Synthron/S65/Hardware/modules/Bus_Card/modules_3d/LPT.step

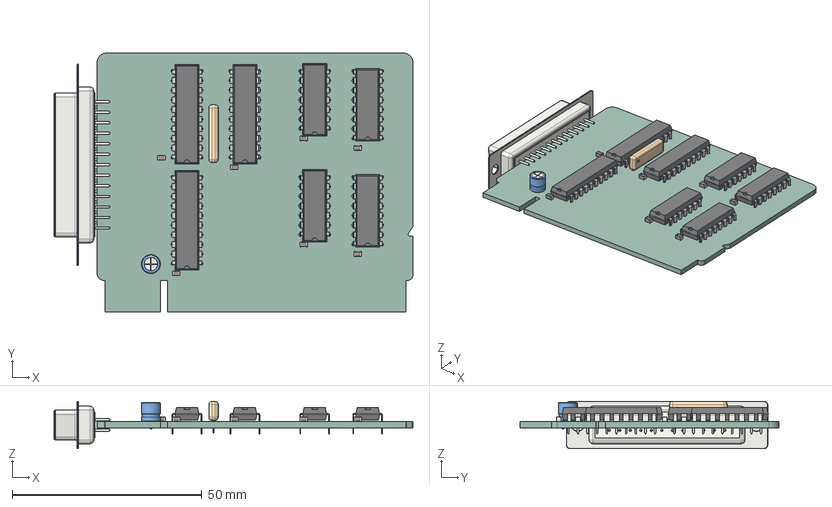
[picture p15: CAD file, 2024-07-26]
Hardware/modules/Bus_Card/modules_3d/LPT.step
94.6 x 68.2 x 12.5 mm
C_0805_2012Metric x 7
DIP-20_W7.62mm x 3
DIP-16_W7.62mm x 2
DIP-14_W7.62mm x 2
R_Array_SIP6
CP_Radial_D50mm_P250mm
DSUB-25_Female_Vertical_P2.77x2.84mm
LPT_PCB
