Synthron/S65/Hardware/modules/Bus_Card/modules_3d/CPU.step

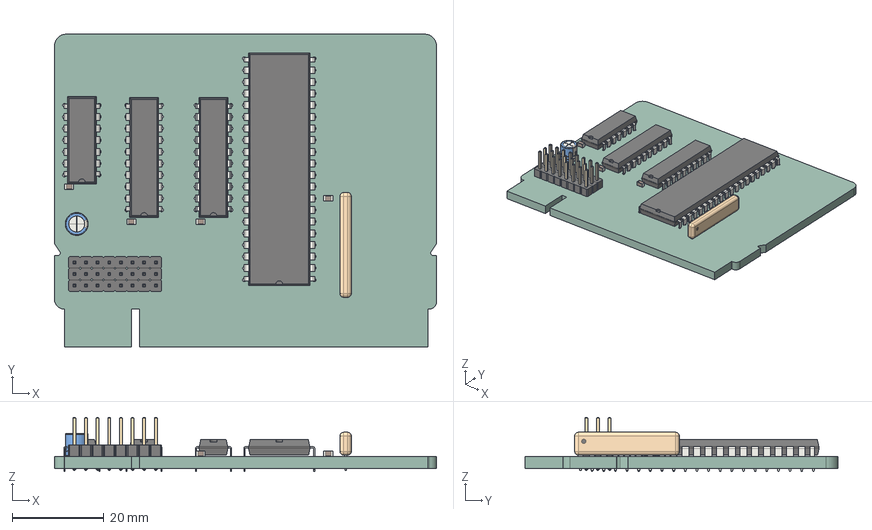
[picture p16: CAD file, 2024-07-26]
Hardware/modules/Bus_Card/modules_3d/CPU.step
83.3 x 68.2 x 11.8 mm
PinHeader_1x08_P254mm_Vertical x 3
DIP-40_W15.24mm
C_0805_2012Metric x 4
CP_Radial_D50mm_P250mm
DIP-20_W7.62mm x 2
DIP-14_W7.62mm
R_Array_SIP9
CPU_PCB
