Synthron/S65/Hardware/modules/IDE-Simple/IDE-Simple.kicad_pcb

## KiCad design Hardware/modules/IDE-Simple/IDE-Simple.kicad_pcb (2024-07-26)

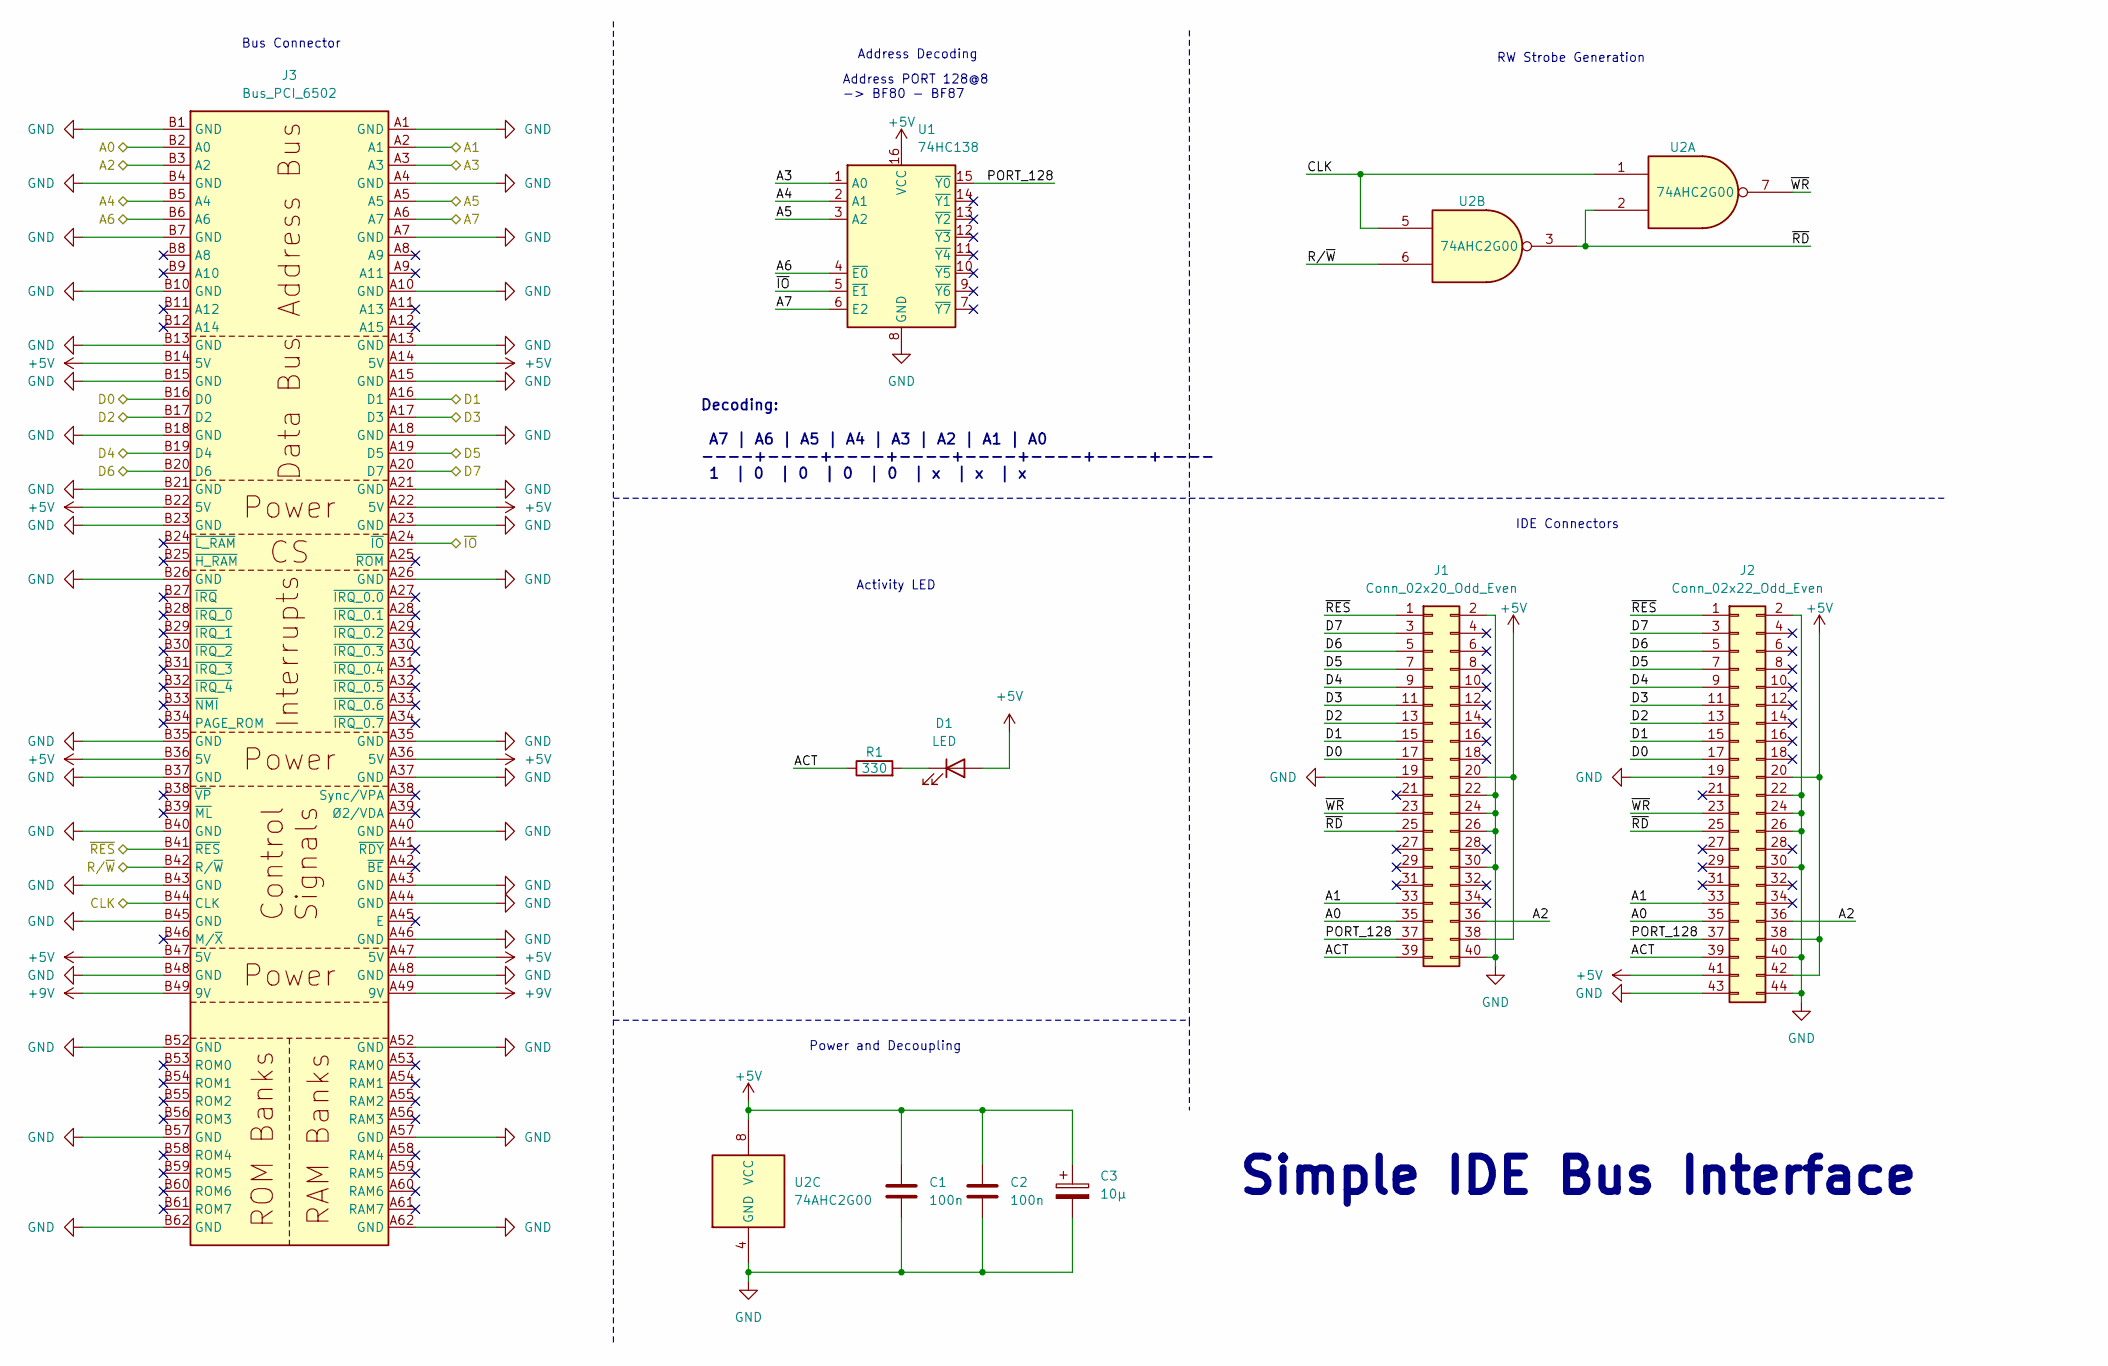
[picture p40: schematic IDE-Simple.kicad_sch, S65xx Computer System]

Parts:
C1, C2: 100n; C_0805_2012Metric
C3: 10µ; CP_Radial_D5.0mm_P2.50mm
D1: LED; LED_0805_2012Metric
J1: Conn_02x20_Odd_Even; IDC-Header_2x20_P2.54mm_Vertical
J2: Conn_02x22_Odd_Even; PinHeader_2x22_P2.00mm_Vertical
J3: Bus_PCI_6502; BUS_PCI
R1: 330; R_0805_2012Metric
U1: 74HC138; DIP-16_W7.62mm
U2: 74AHC2G00; TSSOP-8_3x3mm_P0.65mm

Connections:
+5V: C1.1, C2.1, C3.1, D1.2 (A), J1.20, J1.38, J2.20, J2.38, J2.41, J2.42, J3.A14 (5V), J3.A22 (5V), J3.A36 (5V), J3.A47 (5V), J3.B14 (5V), J3.B22 (5V), J3.B36 (5V), J3.B47 (5V), U1.16 (VCC), U2.8 (VCC)
+9V: J3.A49 (9V), J3.B49 (9V)
/A0: J1.35, J2.35, J3.B2 (A0)
/A1: J1.33, J2.33, J3.A2 (A1)
/A2: J1.36, J2.36, J3.B3 (A2)
/A3: J3.A3, U1.1 (A0)
/A4: J3.B5 (A4), U1.2 (A1)
/A5: J3.A5, U1.3 (A2)
/A6: J3.B6 (A6), U1.4 (~E0)
/A7: J3.A6 (A7), U1.6 (E2)
/ACT: J1.39, J2.39, R1.1
/CLK: J3.B44 (CLK), U2.1, U2.5
/D0: J1.17, J2.17, J3.B16 (D0)
/D1: J1.15, J2.15, J3.A16 (D1)
/D2: J1.13, J2.13, J3.B17 (D2)
/D3: J1.11, J2.11, J3.A17 (D3)
/D4: J1.9, J2.9, J3.B19 (D4)
/D5: J1.7, J2.7, J3.A19 (D5)
/D6: J1.5, J2.5, J3.B20 (D6)
/D7: J1.3, J2.3, J3.A20 (D7)
/PORT_128: J1.37, J2.37, U1.15 (~Y0)
/R/~W: J3.B42 (R/~W), U2.6
/~IO: J3.A24 (~IO), U1.5 (~E1)
/~RD: J1.25, J2.25, U2.2, U2.3
/~RES: J1.1, J2.1, J3.B41 (~RES)
/~WR: J1.23, J2.23, U2.7
GND: C1.2, C2.2, C3.2, J1.2, J1.19, J1.22, J1.24, J1.26, J1.30, J1.40, J2.2, J2.19, J2.22, J2.24, J2.26, J2.30, J2.40, J2.43, J2.44, J3.A1 (GND), J3.A4 (GND), J3.A7 (GND), J3.A10 (GND), J3.A13 (GND), J3.A15 (GND), J3.A18 (GND), J3.A21 (GND), J3.A23 (GND), J3.A26 (GND), J3.A35 (GND), J3.A37 (GND), J3.A40 (GND), J3.A43 (GND), J3.A44 (GND), J3.A46 (GND), J3.A48 (GND), J3.A52 (GND), J3.A57 (GND), J3.A62 (GND), J3.B1 (GND), J3.B4 (GND), J3.B7 (GND), J3.B10 (GND), J3.B13 (GND), J3.B15 (GND), J3.B18 (GND), J3.B21 (GND), J3.B23 (GND), J3.B26 (GND), J3.B35 (GND), J3.B37 (GND), J3.B40 (GND), J3.B43 (GND), J3.B45 (GND), J3.B48 (GND), J3.B52 (GND), J3.B57 (GND), J3.B62 (GND), U1.8 (GND), U2.4 (GND)

Notes on the sheet:
Address Decoding
Activity LED
Bus Connector
Address PORT 128@8 -> BF80 - BF87
Power and Decoupling
Decoding: A7 | A6 | A5 | A4 | A3 | A2 | A1 | A0 ----+----+----+----+----+----+----+---- 1 | 0 | 0 | 0 | 0 | x | x | x
IDE Connectors
RW Strobe Generation
Simple IDE Bus Interface

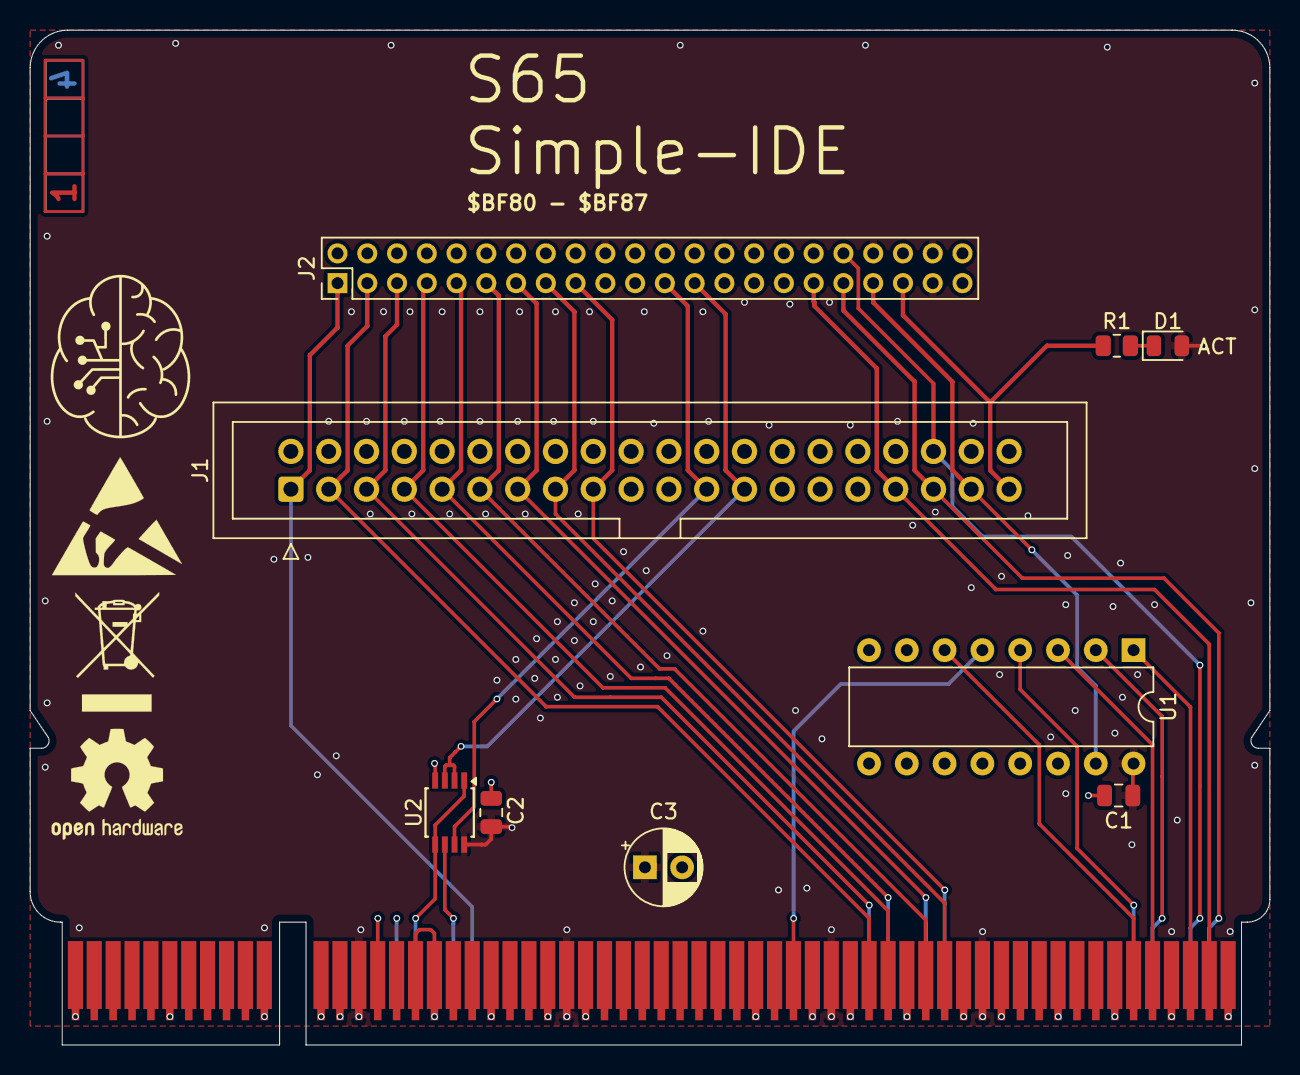
[picture p41: board IDE-Simple.kicad_pcb from above]

Board: 4 copper layers, 83.3 x 68.2 mm, 11 parts (1 on the bottom side), 27 nets.

Other parts of the board:
Ref**: Val**; ladder_4
