Synthron/S65/Hardware/modules/CF/CF.kicad_pcb

## KiCad design Hardware/modules/CF/CF.kicad_pcb (2024-07-26)

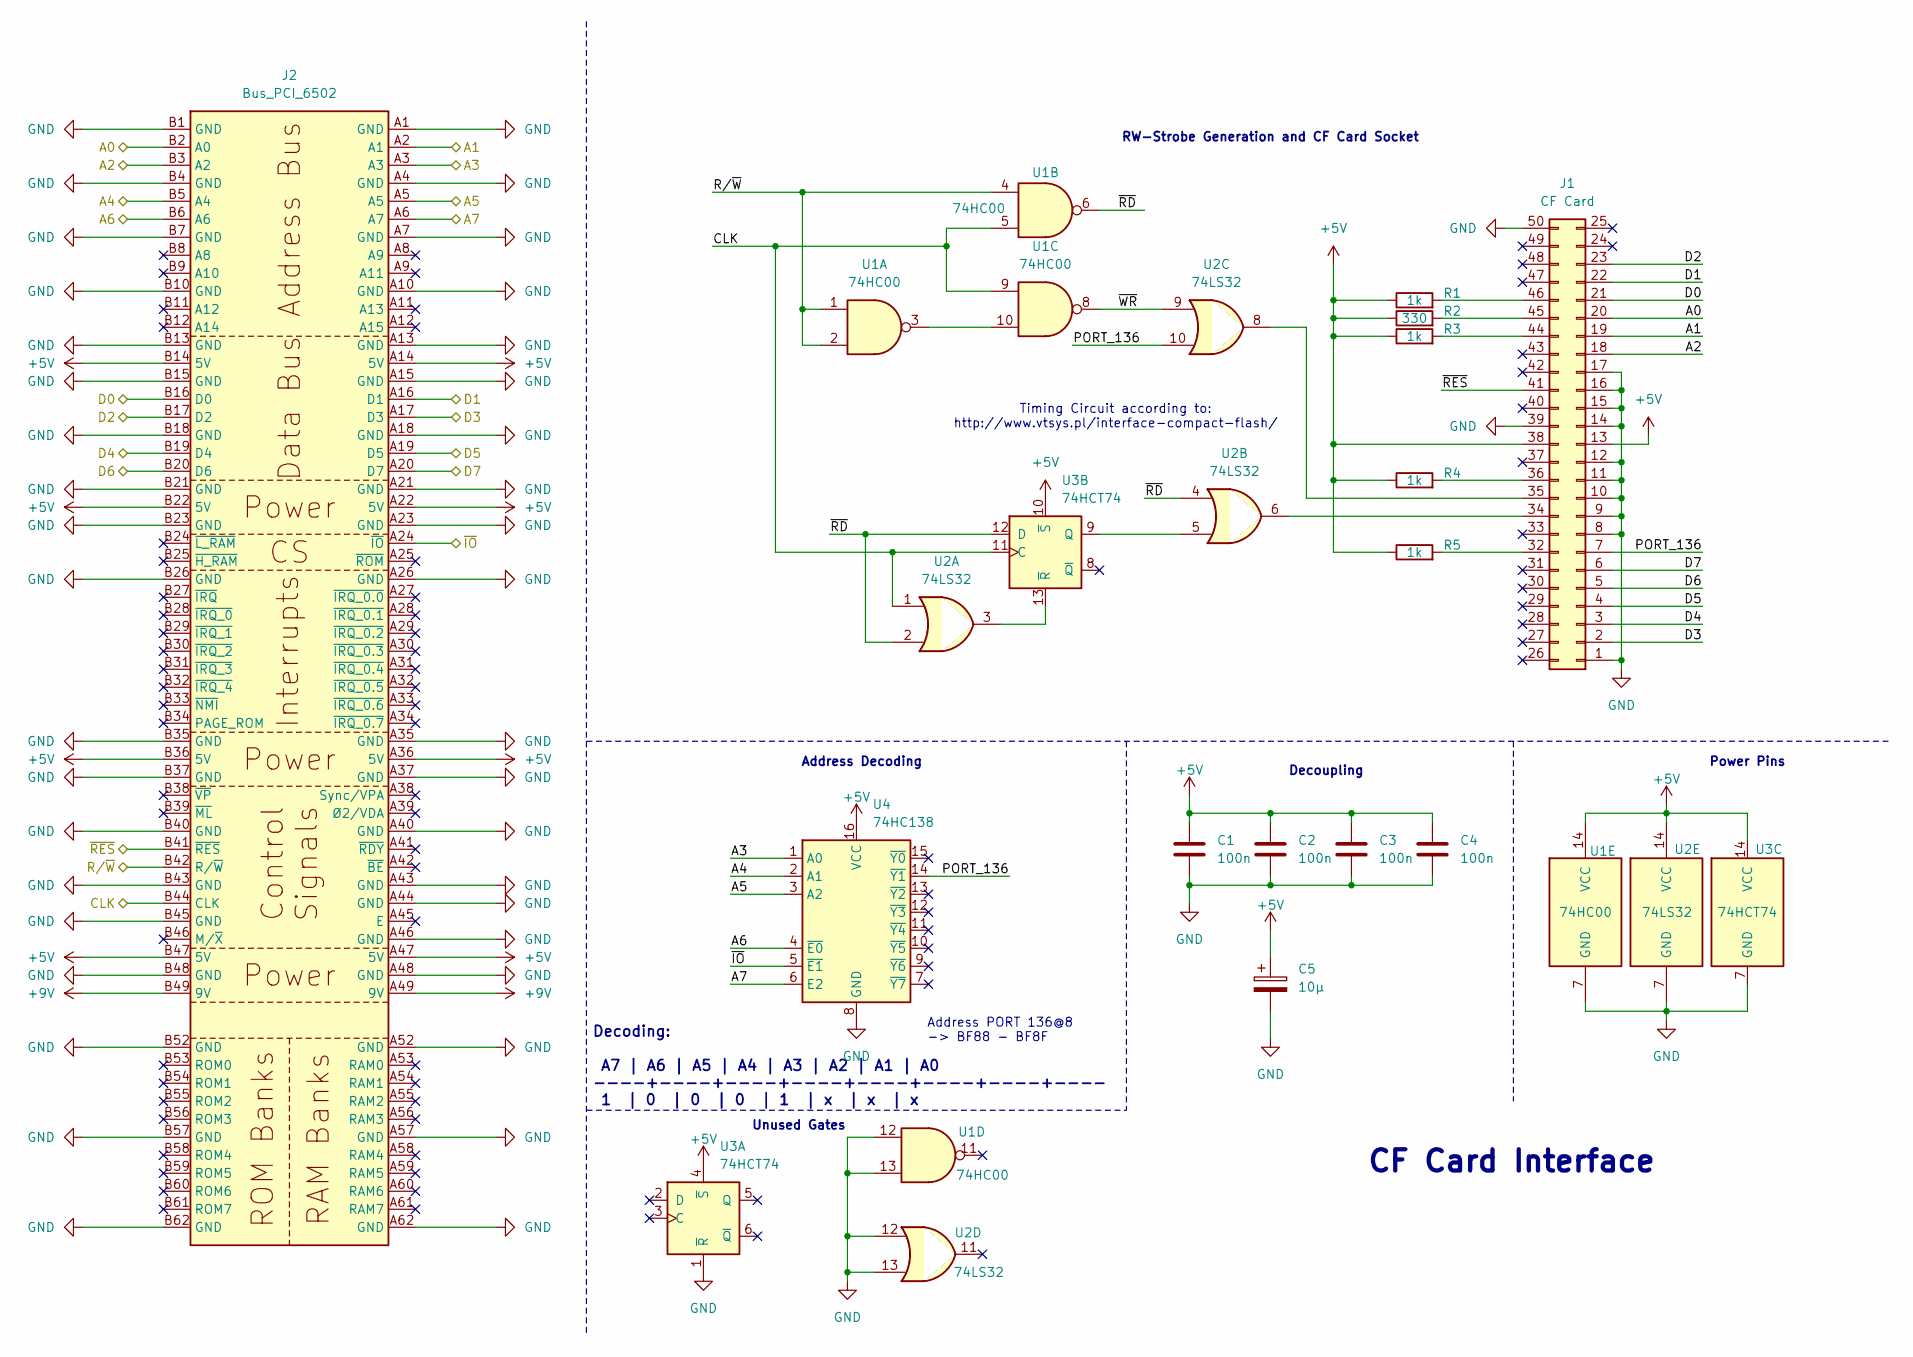
[picture p42: schematic CF.kicad_sch, S65xx Computer System]

Parts:
C1, C2, C3, C4: 100n; C_0805_2012Metric
C5: 10µ; CP_Radial_D5.0mm_P2.50mm
J1: CF Card; CF-Card_3M_N7E50-A516xx-30
J2: Bus_PCI_6502; BUS_PCI
R1, R3, R4, R5: 1k; R_0805_2012Metric
R2: 330; R_0805_2012Metric
U1: 74HC00; DIP-14_W7.62mm
U2: 74LS32; DIP-14_W7.62mm
U3: 74HCT74; DIP-14_W7.62mm
U4: 74HC138; DIP-16_W7.62mm

Connections:
+5V: C1.1, C2.1, C3.1, C4.1, C5.1, J1.13, J1.38, J2.A14 (5V), J2.A22 (5V), J2.A36 (5V), J2.A47 (5V), J2.B14 (5V), J2.B22 (5V), J2.B36 (5V), J2.B47 (5V), R1.1, R2.1, R3.1, R4.1, R5.1, U1.14 (VCC), U2.14 (VCC), U3.4 (~S), U3.10 (~S), U3.14 (VCC), U4.16 (VCC)
+9V: J2.A49 (9V), J2.B49 (9V)
/A0: J1.20, J2.B2 (A0)
/A1: J1.19, J2.A2 (A1)
/A2: J1.18, J2.B3 (A2)
/A3: J2.A3, U4.1 (A0)
/A4: J2.B5 (A4), U4.2 (A1)
/A5: J2.A5, U4.3 (A2)
/A6: J2.B6 (A6), U4.4 (~E0)
/A7: J2.A6 (A7), U4.6 (E2)
/CLK: J2.B44 (CLK), U1.5, U1.9, U2.1, U3.11 (C)
/D0: J1.21, J2.B16 (D0)
/D1: J1.22, J2.A16 (D1)
/D2: J1.23, J2.B17 (D2)
/D3: J1.2, J2.A17 (D3)
/D4: J1.3, J2.B19 (D4)
/D5: J1.4, J2.A19 (D5)
/D6: J1.5, J2.B20 (D6)
/D7: J1.6, J2.A20 (D7)
/PORT_136: J1.7, U2.10, U4.14 (~Y1)
/R/~W: J2.B42 (R/~W), U1.1, U1.2, U1.4
/~IO: J2.A24 (~IO), U4.5 (~E1)
/~RD: U1.6, U2.2, U2.4, U3.12 (D)
/~RES: J1.41, J2.B41 (~RES)
/~WR: U1.8, U2.9
GND: C1.2, C2.2, C3.2, C4.2, C5.2, J1.1, J1.8, J1.9, J1.10, J1.11, J1.12, J1.14, J1.15, J1.16, J1.17, J1.39, J1.50, J2.A1 (GND), J2.A4 (GND), J2.A7 (GND), J2.A10 (GND), J2.A13 (GND), J2.A15 (GND), J2.A18 (GND), J2.A21 (GND), J2.A23 (GND), J2.A26 (GND), J2.A35 (GND), J2.A37 (GND), J2.A40 (GND), J2.A43 (GND), J2.A44 (GND), J2.A46 (GND), J2.A48 (GND), J2.A52 (GND), J2.A57 (GND), J2.A62 (GND), J2.B1 (GND), J2.B4 (GND), J2.B7 (GND), J2.B10 (GND), J2.B13 (GND), J2.B15 (GND), J2.B18 (GND), J2.B21 (GND), J2.B23 (GND), J2.B26 (GND), J2.B35 (GND), J2.B37 (GND), J2.B40 (GND), J2.B43 (GND), J2.B45 (GND), J2.B48 (GND), J2.B52 (GND), J2.B57 (GND), J2.B62 (GND), U1.7 (GND), U1.12, U1.13, U2.7 (GND), U2.12, U2.13, U3.1 (~R), U3.7 (GND), U4.8 (GND)
unnamed: J1.32, R5.2
unnamed: J1.34, U2.6
unnamed: J1.35, U2.8
unnamed: J1.36, R4.2
unnamed: J1.44, R3.2
unnamed: J1.45, R2.2
unnamed: J1.46, R1.2
unnamed: U1.3, U1.10
unnamed: U2.5, U3.9 (Q)
unnamed: U2.3, U3.13 (~R)

Notes on the sheet:
Decoding: A7 | A6 | A5 | A4 | A3 | A2 | A1 | A0 ----+----+----+----+----+----+----+---- 1 | 0 | 0 | 0 | 1 | x | x | x
Power Pins
Address Decoding
Decoupling
CF Card Interface
Address PORT 136@8 -> BF88 - BF8F
Timing Circuit according to: http://www.vtsys.pl/interface-compact-flash/
RW-Strobe Generation and CF Card Socket
Unused Gates
