Synthron/S65/Hardware/modules/CF/CF.kicad_pcb

## KiCad design Hardware/modules/CF/CF.kicad_pcb (continued)

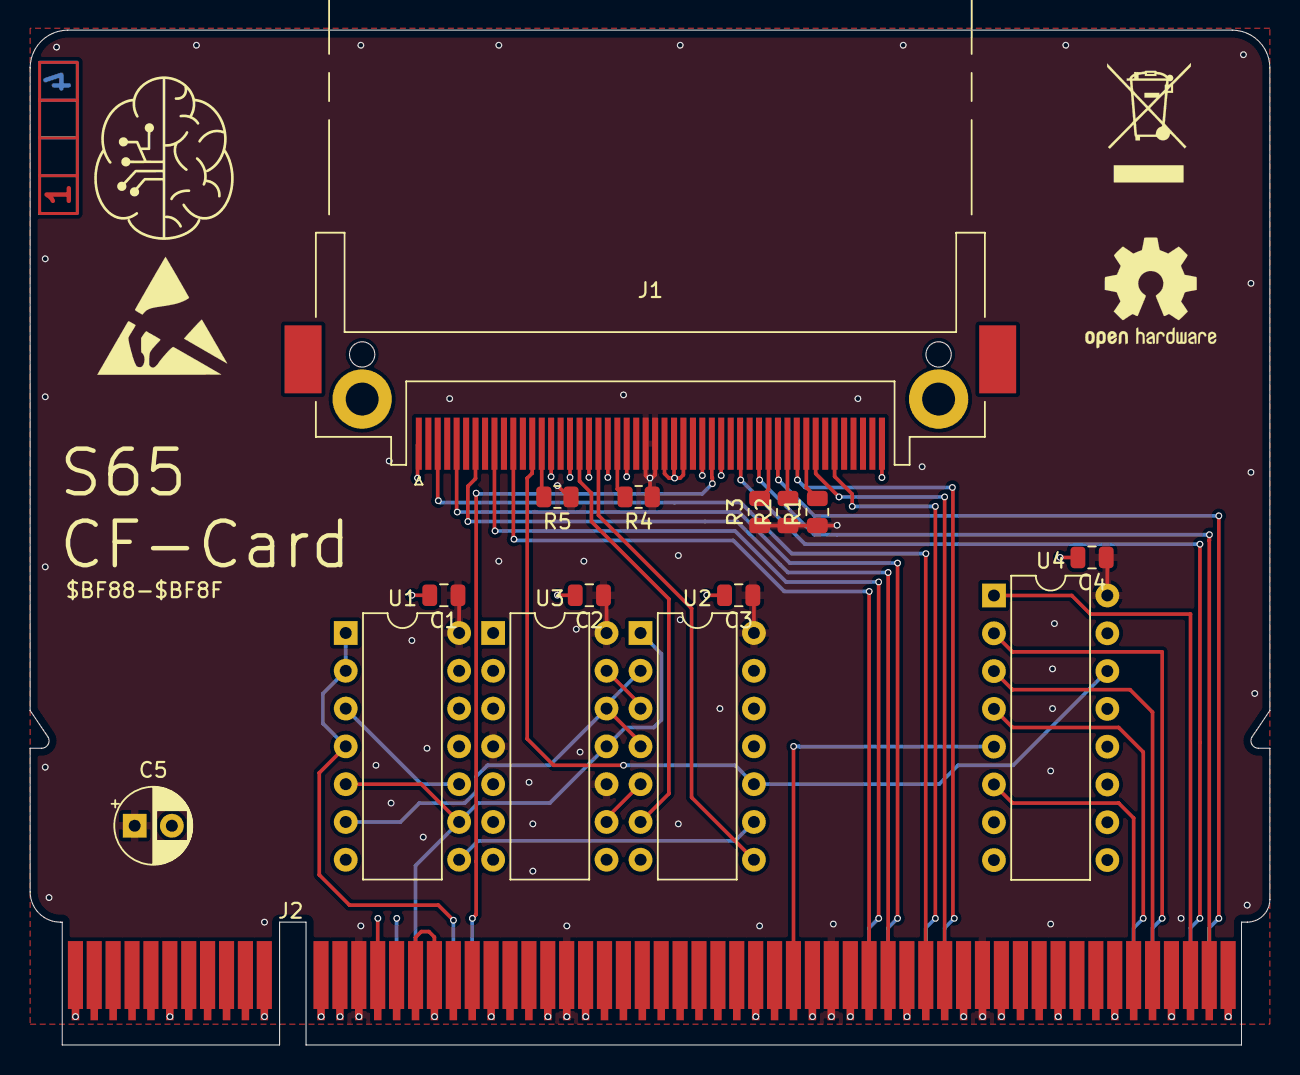
[picture p43: board CF.kicad_pcb from above]

Board: 4 copper layers, 83.3 x 68.2 mm, 17 parts (1 on the bottom side), 36 nets.

Other parts of the board:
Ref**: Val**; ladder_4
