Synthron/S65/Hardware/modules/IDE/IDE.kicad_pcb

## KiCad design Hardware/modules/IDE/IDE.kicad_pcb (2024-07-26)

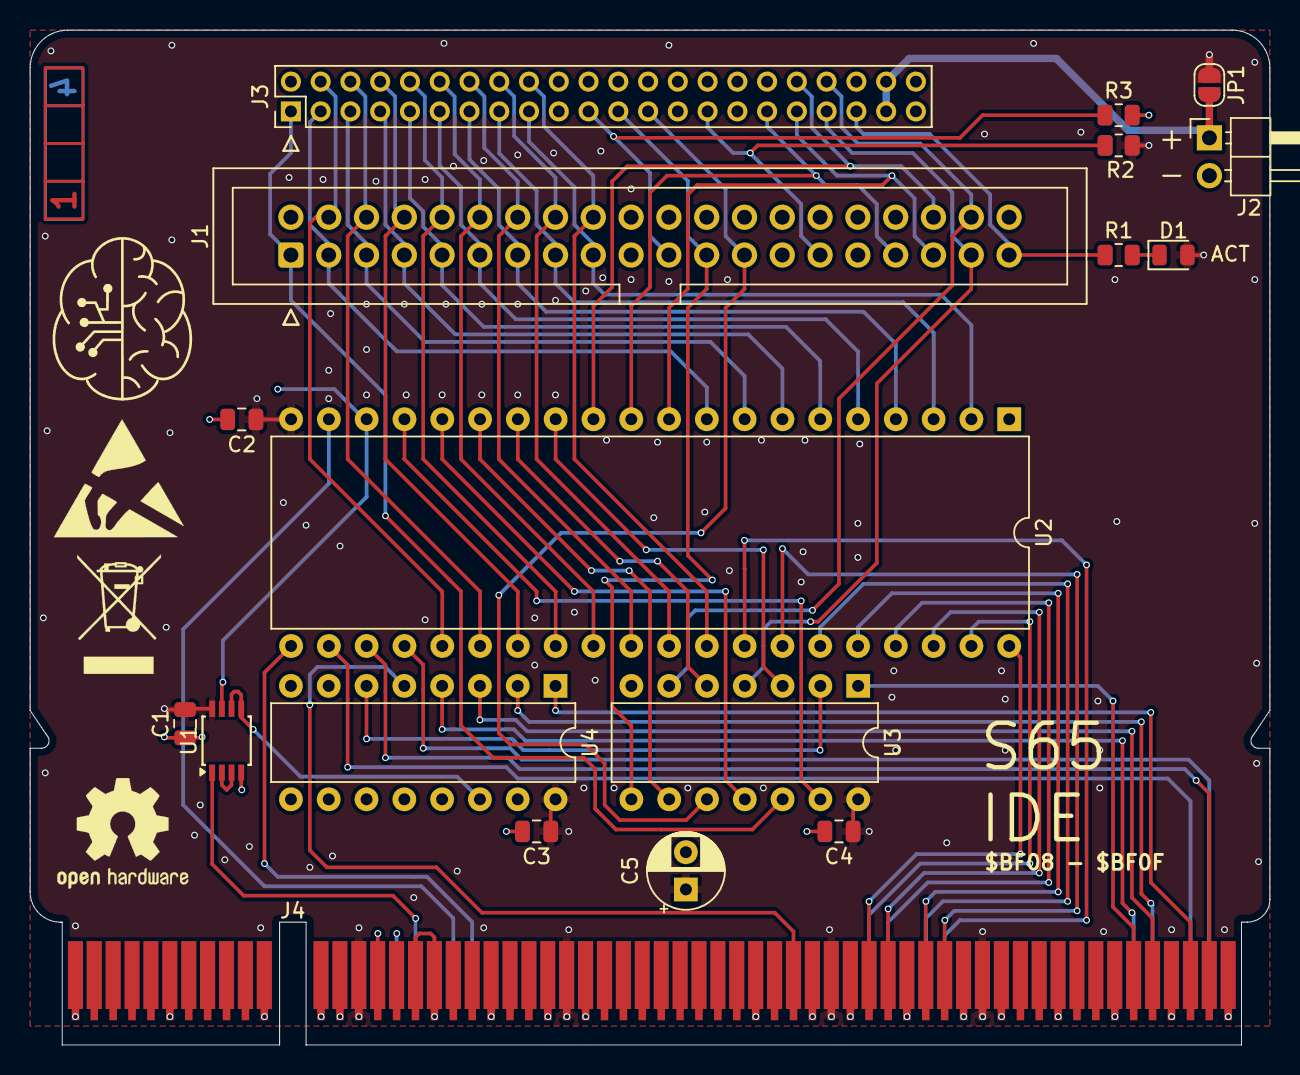
[picture p44: board IDE.kicad_pcb from above]

Board: 4 copper layers, 83.3 x 68.2 mm, 19 parts (1 on the bottom side), 53 nets.

Parts:
C1, C2, C3, C4: 100n; C_0805_2012Metric
C5: 10µ; CP_Radial_D5.0mm_P2.50mm
D1: LED; LED_0805_2012Metric
J1: Conn_02x20_Odd_Even; IDC-Header_2x20_P2.54mm_Vertical
J2: IDE_VCC; PinHeader_1x02_P2.54mm_Horizontal
J3: Conn_02x22_Odd_Even; PinHeader_2x22_P2.00mm_Vertical
J4: Bus_PCI_6502; BUS_PCI
JP1: Jumper_2_Open; SolderJumper-2_P1.3mm_Open_RoundedPad1.0x1.5mm
R1: 330; R_0805_2012Metric
R2, R3: 10k; R_0805_2012Metric
Ref**: Val**; ladder_4
U1: 74AHC2G00; TSSOP-8_3x3mm_P0.65mm
U2: 6525; DIP-40_W15.24mm
U3: 74HCT04; DIP-14_W7.62mm
U4: 74HC138; DIP-16_W7.62mm

Connections:
+5V: C1.1, C2.1, C3.1, C4.1, C5.1, D1.2 (A), J4.A14 (5V), J4.A22 (5V), J4.A36 (5V), J4.A47 (5V), J4.B14 (5V), J4.B22 (5V), J4.B36 (5V), J4.B47 (5V), JP1.1 (A), R2.2, U1.8 (VCC), U2.20 (VDD), U3.14 (VCC), U4.16 (VCC)
+9V: J4.A49 (9V), J4.B49 (9V)
/A0: J4.B2 (A0), U2.24 (RS0)
/A1: J4.A2 (A1), U2.23 (RS1)
/A2: J4.B3 (A2), U2.22 (RS2)
/A3: J4.A3, U4.1 (A0)
/A4: J4.B5 (A4), U4.2 (A1)
/A5: J4.A5, U4.3 (A2)
/A6: J4.B6 (A6), U4.4 (~E0)
/A7: J4.A6 (A7), U3.1
/ACT: J1.39, J3.39, R1.1
/CLK: J4.B44 (CLK), U1.1
/D0: J4.B16 (D0), U2.33 (D0)
/D1: J4.A16 (D1), U2.34 (D1)
/D2: J4.B17 (D2), U2.35 (D2)
/D3: J4.A17 (D3), U2.36 (D3)
/D4: J4.B19 (D4), U2.37 (D4)
/D5: J4.A19 (D5), U2.38 (D5)
/D6: J4.B20 (D6), U2.39 (D6)
/D7: J4.A20 (D7), U2.40 (D7)
/DA0: J1.35, J3.35, U2.10 (PB0)
/DA1: J1.33, J3.33, U2.11 (PB1)
/DA2: J1.36, J3.36, U2.12 (PB2)
/DCS0: J1.37, J3.37, U3.4
/DCS1: J1.38, J3.38, U3.6
/DIOR: J1.25, J3.25, U3.10
/DIOW: J1.23, J3.23, U3.8
/DMACK: J1.29, J3.29, R2.1
/DMARQ: J1.21, J3.21, R3.1
/DRESET: J1.1, J3.1, U3.12
/IDEVCC: J2.1, J3.41, J3.42, JP1.2 (B)
/PA0: J1.17, J3.17, U2.2 (PA0)
/PA1: J1.15, J3.15, U2.3 (PA1)
/PA2: J1.13, J3.13, U2.4 (PA2)
/PA3: J1.11, J3.11, U2.5 (PA3)
/PA4: J1.9, J3.9, U2.6 (PA4)
/PA5: J1.7, J3.7, U2.7 (PA5)
/PA6: J1.5, J3.5, U2.8 (PA6)
/PA7: J1.3, J3.3, U2.9 (PA7)
/PB0: J1.4, J3.4, U2.25 (PC0)
/PB1: J1.6, J3.6, U2.26 (PC1)
/PB2: J1.8, J3.8, U2.27 (PC2)
/PB3: J1.10, J3.10, U2.28 (PC3)
/PB4: J1.12, J3.12, U2.29 (PC4)
/PB5: J1.14, J3.14, U2.30 (PC5)
/PB6: J1.16, J3.16, U2.31 (PC6)
/PB7: J1.18, J3.18, U2.32 (PC7)
/PORT_8: U1.2, U1.3
/R/~W: J4.B42 (R/~W), U2.19 (R/~W)
/~IO: J4.A24 (~IO), U4.5 (~E1)
/~RES: J4.B41 (~RES), U2.21 (~RST)
GND: C1.2, C2.2, C3.2, C4.2, C5.2, J1.2, J1.19, J1.22, J1.24, J1.26, J1.28, J1.30, J1.40, J2.2, J3.2, J3.19, J3.22, J3.24, J3.26, J3.28, J3.30, J3.40, J3.43, J3.44, J4.A1 (GND), J4.A4 (GND), J4.A7 (GND), J4.A10 (GND), J4.A13 (GND), J4.A15 (GND), J4.A18 (GND), J4.A21 (GND), J4.A23 (GND), J4.A26 (GND), J4.A35 (GND), J4.A37 (GND), J4.A40 (GND), J4.A43 (GND), J4.A44 (GND), J4.A46 (GND), J4.A48 (GND), J4.A52 (GND), J4.A57 (GND), J4.A62 (GND), J4.B1 (GND), J4.B4 (GND), J4.B7 (GND), J4.B10 (GND), J4.B13 (GND), J4.B15 (GND), J4.B18 (GND), J4.B21 (GND), J4.B23 (GND), J4.B26 (GND), J4.B35 (GND), J4.B37 (GND), J4.B40 (GND), J4.B43 (GND), J4.B45 (GND), J4.B48 (GND), J4.B52 (GND), J4.B57 (GND), J4.B62 (GND), R3.2, U1.4 (GND), U2.1 (VSS), U3.7 (GND), U4.8 (GND)
unnamed: U1.5, U1.6, U4.14 (~Y1)
