Synthron/S65/Hardware/modules/LPT/LPT.kicad_pcb

## KiCad design Hardware/modules/LPT/LPT.kicad_pcb (2024-07-26)

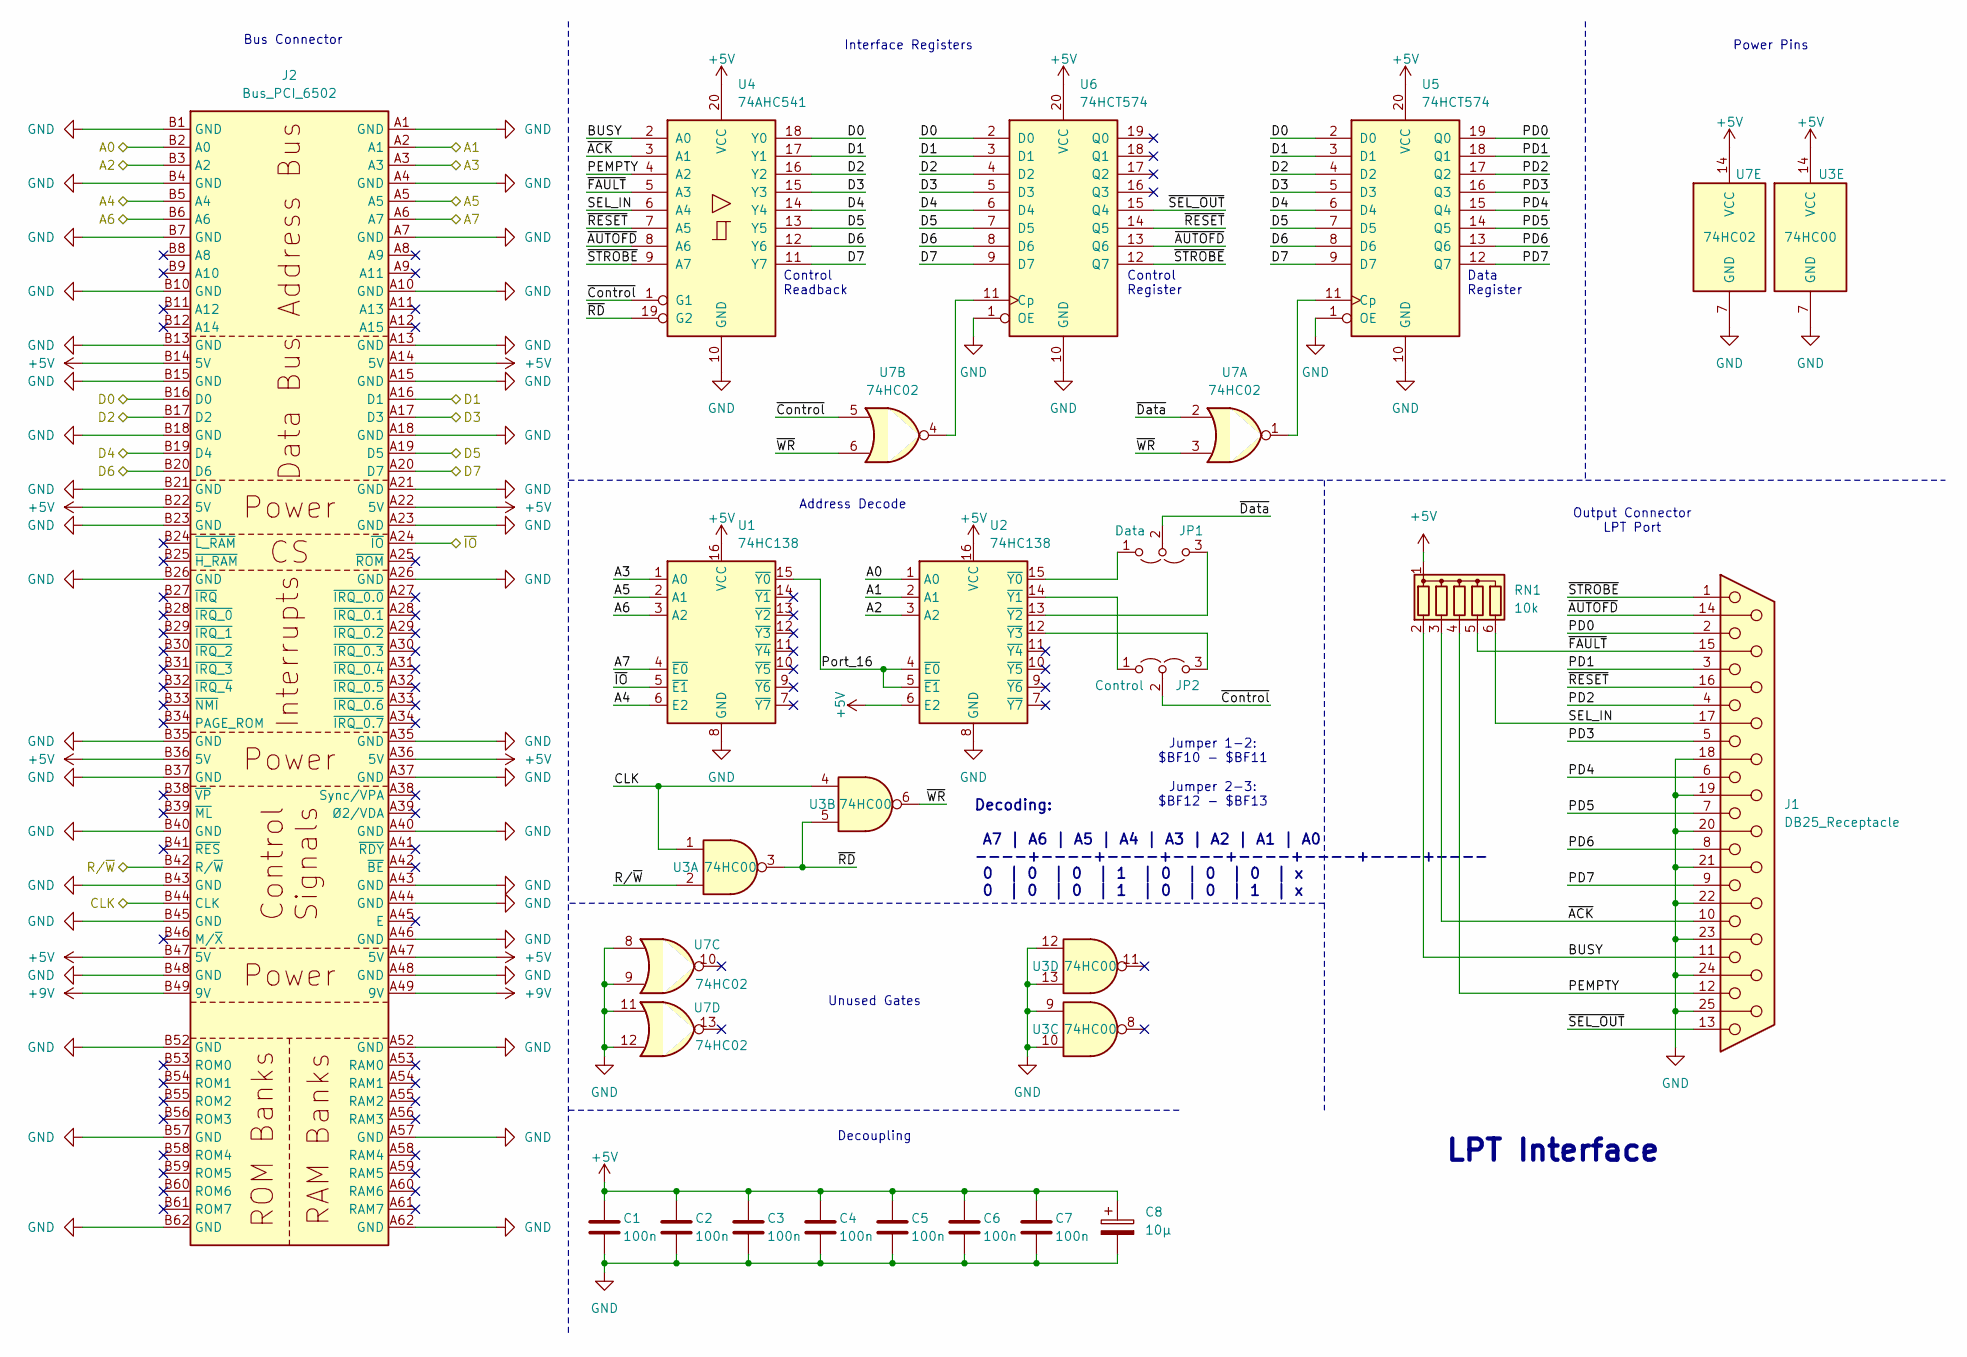
[picture p45: schematic LPT.kicad_sch, S65xx Computer System]

Parts:
C1, C2, C3, C4, C5, C6, C7: 100n; C_0805_2012Metric
C8: 10µ; CP_Radial_D5.0mm_P2.50mm
J1: DB25_Receptacle; DSUB-25_Female_EdgeMount_P2.77mm
J2: Bus_PCI_6502; BUS_PCI
JP1: Data; SolderJumper-3_P2.0mm_Open_TrianglePad1.0x1.5mm_NumberLabels
JP2: Control; SolderJumper-3_P2.0mm_Open_TrianglePad1.0x1.5mm_NumberLabels
RN1: 10k; R_Array_SIP6
U1, U2: 74HC138; DIP-16_W7.62mm
U3: 74HC00; DIP-14_W7.62mm
U4: 74AHC541; DIP-20_W7.62mm
U5, U6: 74HCT574; DIP-20_W7.62mm
U7: 74HC02; DIP-14_W7.62mm

Connections:
+5V: C1.1, C2.1, C3.1, C4.1, C5.1, C6.1, C7.1, C8.1, J2.A14 (5V), J2.A22 (5V), J2.A36 (5V), J2.A47 (5V), J2.B14 (5V), J2.B22 (5V), J2.B36 (5V), J2.B47 (5V), RN1.1 (common), U1.16 (VCC), U2.6 (E2), U2.16 (VCC), U3.14 (VCC), U4.20 (VCC), U5.20 (VCC), U6.20 (VCC), U7.14 (VCC)
+9V: J2.A49 (9V), J2.B49 (9V)
/A0: J2.B2 (A0), U2.1 (A0)
/A1: J2.A2 (A1), U2.2 (A1)
/A2: J2.B3 (A2), U2.3 (A2)
/A3: J2.A3, U1.1 (A0)
/A4: J2.B5 (A4), U1.6 (E2)
/A5: J2.A5, U1.2 (A1)
/A6: J2.B6 (A6), U1.3 (A2)
/A7: J2.A6 (A7), U1.4 (~E0)
/BUSY: J1.11, RN1.2 (R1), U4.2 (A0)
/CLK: J2.B44 (CLK), U3.1, U3.4
/D0: J2.B16 (D0), U4.18 (Y0), U5.2 (D0), U6.2 (D0)
/D1: J2.A16 (D1), U4.17 (Y1), U5.3 (D1), U6.3 (D1)
/D2: J2.B17 (D2), U4.16 (Y2), U5.4 (D2), U6.4 (D2)
/D3: J2.A17 (D3), U4.15 (Y3), U5.5 (D3), U6.5 (D3)
/D4: J2.B19 (D4), U4.14 (Y4), U5.6 (D4), U6.6 (D4)
/D5: J2.A19 (D5), U4.13 (Y5), U5.7 (D5), U6.7 (D5)
/D6: J2.B20 (D6), U4.12 (Y6), U5.8 (D6), U6.8 (D6)
/D7: J2.A20 (D7), U4.11 (Y7), U5.9 (D7), U6.9 (D7)
/PD0: J1.2, U5.19 (Q0)
/PD1: J1.3, U5.18 (Q1)
/PD2: J1.4, U5.17 (Q2)
/PD3: J1.5, U5.16 (Q3)
/PD4: J1.6, U5.15 (Q4)
/PD5: J1.7, U5.14 (Q5)
/PD6: J1.8, U5.13 (Q6)
/PD7: J1.9, U5.12 (Q7)
/PEMPTY: J1.12, RN1.4 (R3), U4.4 (A2)
/Port_16: U1.15 (~Y0), U2.4 (~E0), U2.5 (~E1)
/R/~W: J2.B42 (R/~W), U3.2
/SEL_IN: J1.17, RN1.6 (R5), U4.6 (A4)
/~ACK: J1.10, RN1.3 (R2), U4.3 (A1)
/~AUTOFD: J1.14, U4.8 (A6), U6.13 (Q6)
/~Control: JP2.2 (C), U4.1 (G1), U7.5
/~Data: JP1.2 (C), U7.2
/~FAULT: J1.15, RN1.5 (R4), U4.5 (A3)
/~IO: J2.A24 (~IO), U1.5 (~E1)
/~RD: U3.3, U3.5, U4.19 (G2)
/~RESET: J1.16, U4.7 (A5), U6.14 (Q5)
/~SEL_OUT: J1.13, U6.15 (Q4)
/~STROBE: J1.1, U4.9 (A7), U6.12 (Q7)
/~WR: U3.6, U7.3, U7.6
GND: C1.2, C2.2, C3.2, C4.2, C5.2, C6.2, C7.2, C8.2, J1.18, J1.19, J1.20, J1.21, J1.22, J1.23, J1.24, J1.25, J2.A1 (GND), J2.A4 (GND), J2.A7 (GND), J2.A10 (GND), J2.A13 (GND), J2.A15 (GND), J2.A18 (GND), J2.A21 (GND), J2.A23 (GND), J2.A26 (GND), J2.A35 (GND), J2.A37 (GND), J2.A40 (GND), J2.A43 (GND), J2.A44 (GND), J2.A46 (GND), J2.A48 (GND), J2.A52 (GND), J2.A57 (GND), J2.A62 (GND), J2.B1 (GND), J2.B4 (GND), J2.B7 (GND), J2.B10 (GND), J2.B13 (GND), J2.B15 (GND), J2.B18 (GND), J2.B21 (GND), J2.B23 (GND), J2.B26 (GND), J2.B35 (GND), J2.B37 (GND), J2.B40 (GND), J2.B43 (GND), J2.B45 (GND), J2.B48 (GND), J2.B52 (GND), J2.B57 (GND), J2.B62 (GND), U1.8 (GND), U2.8 (GND), U3.7 (GND), U3.9, U3.10, U3.12, U3.13, U4.10 (GND), U5.1 (OE), U5.10 (GND), U6.1 (OE), U6.10 (GND), U7.7 (GND), U7.8, U7.9, U7.11, U7.12
unnamed: JP1.1 (A), U2.15 (~Y0)
unnamed: JP1.3 (B), U2.13 (~Y2)
unnamed: JP2.1 (A), U2.14 (~Y1)
unnamed: JP2.3 (B), U2.12 (~Y3)
unnamed: U5.11 (Cp), U7.1
unnamed: U6.11 (Cp), U7.4

Notes on the sheet:
Interface Registers
Decoupling
Jumper 1-2: $BF10 - $BF11 Jumper 2-3: $BF12 - $BF13
Output Connector LPT Port
Decoding: A7 | A6 | A5 | A4 | A3 | A2 | A1 | A0 ----+----+----+----+----+----+----+---- 0 | 0 | 0 | 1 | 0 | 0 | 0 | x 0 | 0 | 0 | 1 | 0 | 0 | 1 | x
Power Pins
Address Decode
Control Register
Bus Connector
Unused Gates
Control Readback
Data Register
LPT Interface

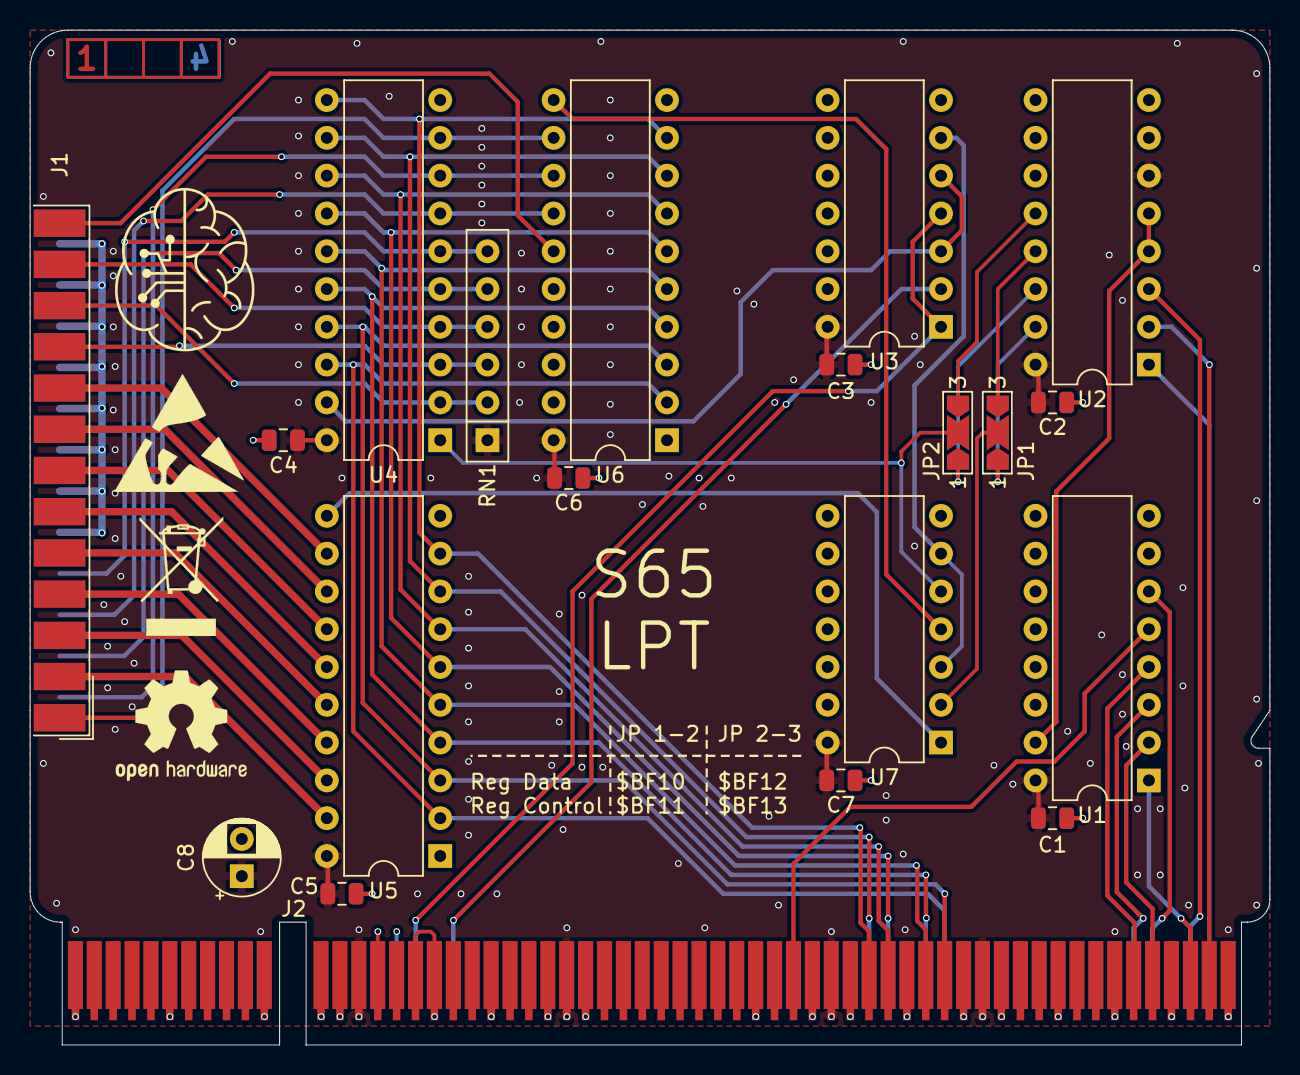
[picture p46: board LPT.kicad_pcb from above]

Board: 4 copper layers, 83.3 x 68.2 mm, 21 parts (1 on the bottom side), 50 nets.

Other parts of the board:
Ref**: Val**; ladder_4
